hsetlik/TunerVCO_STM32/Core/Inc/tuning.h

/*
 * tuning.h
 *
 *  Created on: May 3, 2024
 *      Author: hayden
 */

#ifndef TUNING_H_
#define TUNING_H_

#ifdef __cplusplus
extern "C" {
#endif

#include "stm32g0xx_hal.h"
#include "ssd1306_fonts.h"
#include <stdbool.h>

// alias for what type we should use for the ring buffer heads
typedef uint16_t head_t;

// some constants
#define TUNING_BUF_SIZE 200
#define SEMITONE_RATIO 1.05946309436f
#define IN_TUNE_THRESHOLD 4



// tuning buffer stuff
void triggerTuningUpdate(uint32_t* buffer, head_t* head);
uint32_t getTuningBufferValue(uint32_t* buffer, head_t* head, uint8_t idx);
float getCurrentHz(uint32_t* buffer, head_t* head);
float getPulseWidth(uint32_t* risingBuf, head_t* rHead, uint32_t* fallingBuf, head_t* fHead, uint8_t samplesToCheck);

//-----------------------------------------

// tuning description/display stuff
#define NUM_MIDI_NOTES 128
static float midiNotePitches[NUM_MIDI_NOTES];
static bool midiNotesInitialized;
void initMidiNotePitches();
uint8_t nearestMidiNote(float hz);
int16_t getTuningErrorCents(float hz, uint8_t midiTarget);
// little math helper
bool lowIsCloser(float low, float hi, float target);

//-----------------------------------------

// display
void displayTuning(float hz);


//-----------------------------------------





#ifdef __cplusplus
}
#endif

#endif /* INC_TUNING_H_ */
